luigi-santiago-v/Luli/Luli/Pico/test/LED_and_Motor.py

from machine import Pin
import time

# Setup the GPIO pin for the MOSFET gate control
motor_gate = Pin(21, Pin.OUT)
LED_gate = Pin(22, Pin.OUT)

def motor_on():
    # Setting the gate HIGH will turn on the MOSFET, completing the circuit
    print("MOTOR ON")
    motor_gate.value(1)

def motor_off():
    # Setting the gate LOW will turn off the MOSFET, breaking the circuit
    print("MOTOR OFF")
    motor_gate.value(0)
    
def led_on():
    # Setting the gate HIGH will turn on the MOSFET, completing the circuit
    print("LED ON")
    LED_gate.value(1)

def led_off():
    # Setting the gate LOW will turn off the MOSFET, breaking the circuit
    print("LED OFF")
    LED_gate.value(0)

# Main loop to turn motor on and off
while True:
    motor_on()
    led_on()
    time.sleep(5)  # motor is on for 5 seconds
    motor_off()
    led_off()
    time.sleep(5)
    #time.sleep(5)  # motor is off for 5 seconds
